nicedreamzapp/Heat-N-Clean-Glass-Oven/cad-source/10_Lid_Handle.step

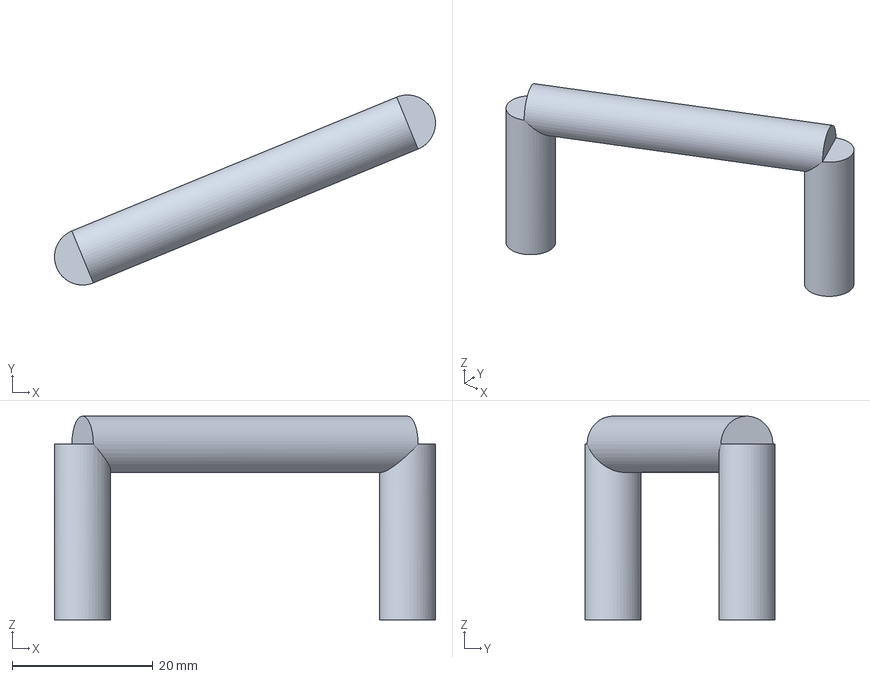
[picture p27: CAD file, 2026-09-28]
cad-source/10_Lid_Handle.step
54.2 x 27.0 x 29.0 mm
