nicedreamzapp/Heat-N-Clean-Glass-Oven/FAB_PACKAGE_2026-09-28/STEP/03_Support_Ring.step

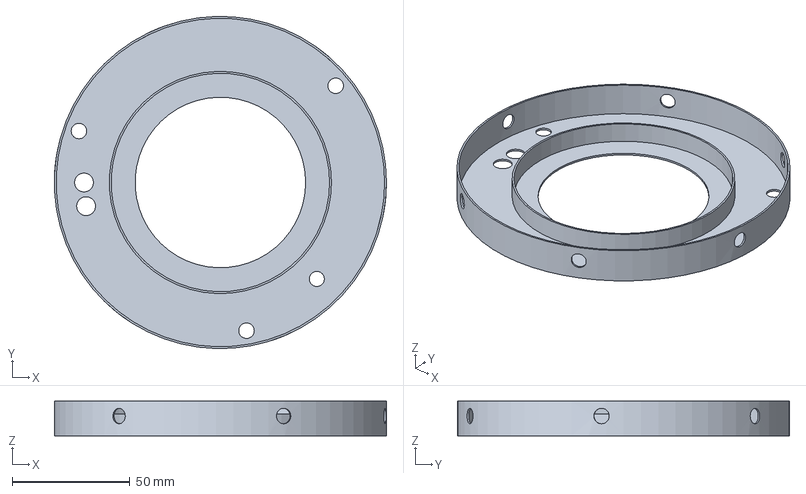
[picture p28: CAD file, 2026-09-30]
FAB_PACKAGE_2026-09-28/STEP/03_Support_Ring.step
141.2 x 141.2 x 14.8 mm
