nicedreamzapp/Heat-N-Clean-Glass-Oven/FAB_PACKAGE_2026-09-28/STEP/09_Lid_Ceramic_Holder.step

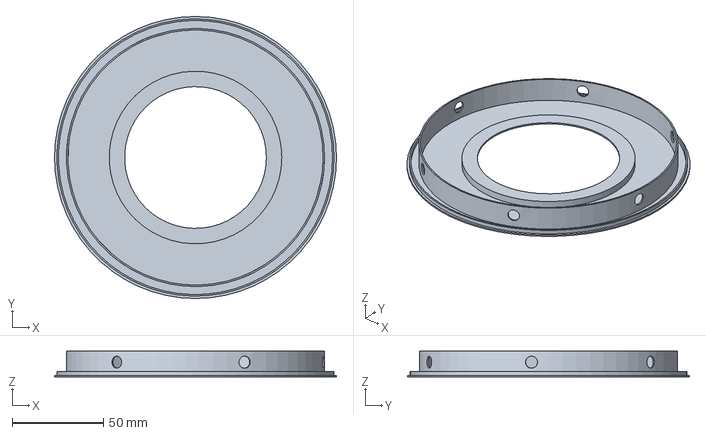
[picture p29: CAD file, 2026-09-30]
FAB_PACKAGE_2026-09-28/STEP/09_Lid_Ceramic_Holder.step
154.4 x 154.4 x 14.0 mm
